LianAarts/Mesh-sensor-network/3D_files/esp32_mesh_node v2.png

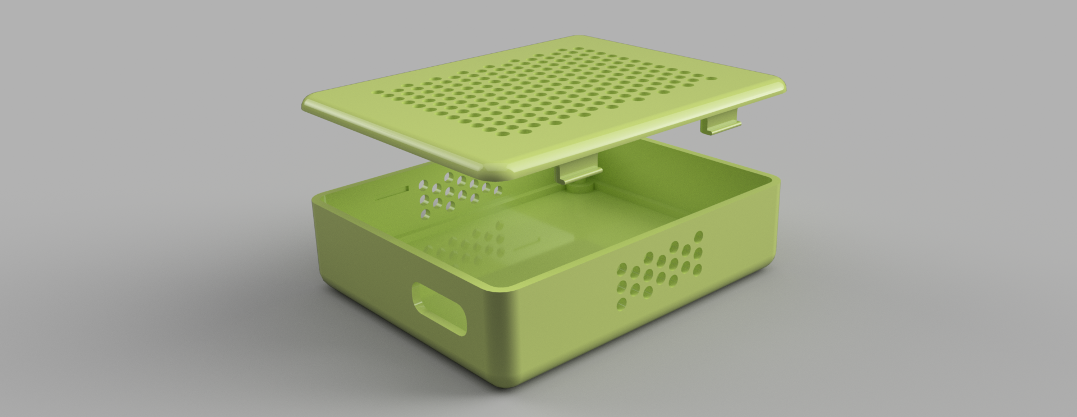
3D_files/esp32_mesh_node v2.png
