LianAarts/Mesh-sensor-network/PCB/PCB0.jpg

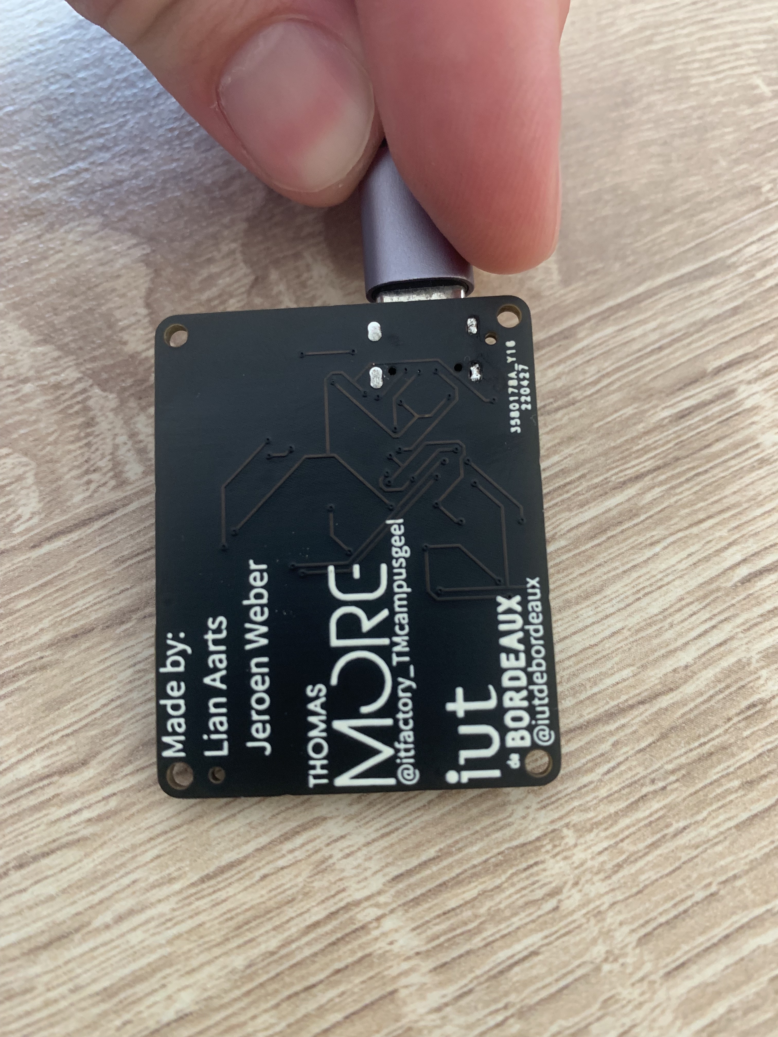
PCB/PCB0.jpg
