LianAarts/Mesh-sensor-network/PCB/PCB1.jpg

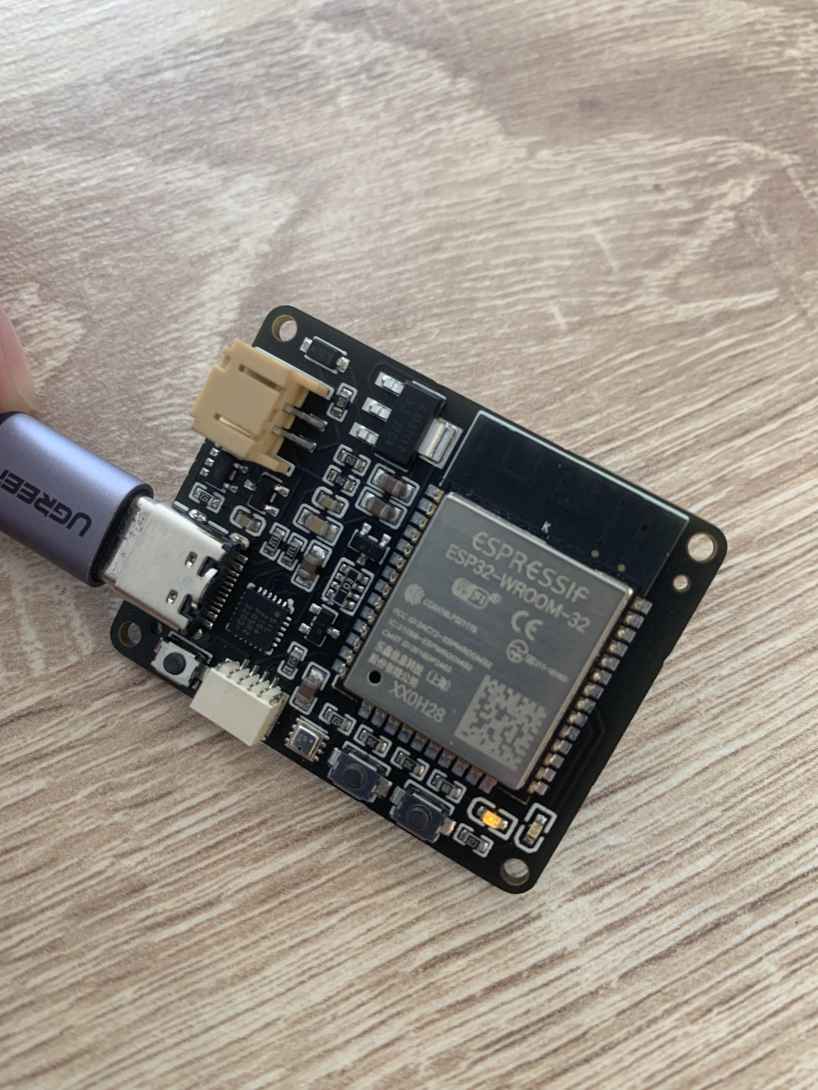
PCB/PCB1.jpg
