LianAarts/Mesh-sensor-network/mesh_node_code/include/rd_22_setup_portal.h

#ifndef rd_22_setup_portal
#define rd_22_setup_portal
#include <Arduino.h>
#include <ESPAsyncWebServer.h>
#include <SPIFFS.h>
#include <DNSServer.h>

void nextDnsRequest();
void setupWebserver();
void endWebserver();

void writeSpiffs(String data, String fileName);
String readSpiffs(String fileName);
#endif
